vwlin/FleetTracker/src/gps.h

#include <driverlib/MSP430F5xx_6xx/gpio.h>
#include <msp430.h>
#include <stdio.h>
#include "SPI.h"

#define SAFEBOOT_DIRECTION           P6DIR
#define SAFEBOOT_PIN                 BIT4
#define SAFEBOOT_SELECT              P6SEL
#define SAFEBOOT_OUTPUT              P6OUT

#define GPS_CS_DIRECTION             P1DIR
#define GPS_CS_PIN                   BIT0
#define GPS_CS_SELECT                P1SEL
#define GPS_CS_OUTPUT                P1OUT

#define SET_SAFEBOOT_AS_GPIO         SAFEBOOT_SELECT &= ~SAFEBOOT_PIN
#define SET_SAFEBOOT_AS_OUTPUT       SAFEBOOT_DIRECTION |= SAFEBOOT_PIN
#define DRIVE_SAFEBOOT_PIN_HIGH      SAFEBOOT_OUTPUT |= SAFEBOOT_PIN
#define DRIVE_SAFEBOOT_PIN_LOW       SAFEBOOT_OUTPUT &= SAFEBOOT_PIN
#define TOGGLE_SAFEBOOT_PIN          SAFEBOOT_OUTPUT ^= SAFEBOOT_PIN

#define SET_GPS_CS_AS_GPIO           GPS_CS_SELECT &= ~GPS_CS_PIN
#define SET_GPS_CS_AS_OUTPUT         GPS_CS_DIRECTION |= GPS_CS_PIN
#define SELECT_GPS_CS                GPS_CS_OUTPUT &= ~GPS_CS_PIN //drive LOW
#define DESELECT_GPS_CS              GPS_CS_OUTPUT |= GPS_CS_PIN //drive HIGH


/* Configure_GPS
 * Drives safeboot high and initializes chip select
 */
void Configure_GPS();


/*~~~~~~~~~~~~~~~~~~~~~~~~~~~~~~~~~~~~~~
 * CONSTRUCT PACKETS
 ~~~~~~~~~~~~~~~~~~~~~~~~~~~~~~~~~~~~~*/

/*
 * ublox_configure_spi_port
 * Builds packet to configure SPI port of ublox module
 *
 * Parameters:
 *  returnPacket - array to be filled with send data
 */
void ublox_configure_spi_port(unsigned char* returnPacket);

/*
 * configure_ublox_nav_pvt
 * Builds packet to request data from ublox module
 *
 * Parameters:
 *  ublox_nav - array to be filled with send data
 */
void configure_ublox_nav_pvt(uint8_t* ublox_nav);

/*
 * configure_ublox_poll
 * Builds packet to configure requesting data from ublox module
 *
 * Parameters:
 *  ublox_poll - array to be filled with send data
 *  id1 - used to classify what to configure on ublox module
 *  id2 - used to classify what to configure on ublox module
 */
void configure_ublox_poll(uint8_t* ublox_poll, uint8_t id1, uint8_t id2);
