vwlin/FleetTracker/src/clock.c

/* --COPYRIGHT--,BSD
 * Copyright (c) 2017, Texas Instruments Incorporated
 * All rights reserved.
 *
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
 * *  Redistributions of source code must retain the above copyright
 *    notice, this list of conditions and the following disclaimer.
 *
 * *  Redistributions in binary form must reproduce the above copyright
 *    notice, this list of conditions and the following disclaimer in the
 *    documentation and/or other materials provided with the distribution.
 *
 * *  Neither the name of Texas Instruments Incorporated nor the names of
 *    its contributors may be used to endorse or promote products derived
 *    from this software without specific prior written permission.
 *
 * THIS SOFTWARE IS PROVIDED BY THE COPYRIGHT HOLDERS AND CONTRIBUTORS "AS IS"
 * AND ANY EXPRESS OR IMPLIED WARRANTIES, INCLUDING, BUT NOT LIMITED TO,
 * THE IMPLIED WARRANTIES OF MERCHANTABILITY AND FITNESS FOR A PARTICULAR
 * PURPOSE ARE DISCLAIMED. IN NO EVENT SHALL THE COPYRIGHT OWNER OR
 * CONTRIBUTORS BE LIABLE FOR ANY DIRECT, INDIRECT, INCIDENTAL, SPECIAL,
 * EXEMPLARY, OR CONSEQUENTIAL DAMAGES (INCLUDING, BUT NOT LIMITED TO,
 * PROCUREMENT OF SUBSTITUTE GOODS OR SERVICES; LOSS OF USE, DATA, OR PROFITS;
 * OR BUSINESS INTERRUPTION) HOWEVER CAUSED AND ON ANY THEORY OF LIABILITY,
 * WHETHER IN CONTRACT, STRICT LIABILITY, OR TORT (INCLUDING NEGLIGENCE OR
 * OTHERWISE) ARISING IN ANY WAY OUT OF THE USE OF THIS SOFTWARE,
 * EVEN IF ADVISED OF THE POSSIBILITY OF SUCH DAMAGE.
 * --/COPYRIGHT--*/

/*********************************************************************************
 * Set clock speed to 16 MHz
 */

//Variable to store status of Oscillator fault flags
//
//*****************************************************************************
#include "clock.h"
uint16_t status;

void Configure_Clock (void)
{
    // Set VCore
    PMM_setVCore(PMM_CORE_LEVEL_0);

    // Set DCO FLL reference = REFO
    UCS_initClockSignal(
        UCS_FLLREF,
        UCS_REFOCLK_SELECT,
        UCS_CLOCK_DIVIDER_1
        );
    // Set ACLK = REFO
    UCS_initClockSignal(
        UCS_ACLK,
        UCS_REFOCLK_SELECT,
        UCS_CLOCK_DIVIDER_1
        );

    // Set Ratio and Desired MCLK Frequency and initialize DCO
    UCS_initFLLSettle(
        UCS_MCLK_DESIRED_FREQUENCY_IN_KHZ,
        UCS_MCLK_FLLREF_RATIO
        );

    // Enable global oscillator fault flag
    SFR_clearInterrupt(SFR_OSCILLATOR_FAULT_INTERRUPT);
    SFR_enableInterrupt(SFR_OSCILLATOR_FAULT_INTERRUPT);

    // Enable global interrupt
    __bis_SR_register(GIE);

}


#if defined(__TI_COMPILER_VERSION__) || defined(__IAR_SYSTEMS_ICC__)
#pragma vector=UNMI_VECTOR
__interrupt
#elif defined(__GNUC__)
__attribute__((interrupt(UNMI_VECTOR)))
#endif
void NMI_ISR(void)
{
  do {
    // If it still can't clear the oscillator fault flags after the timeout, trap and wait here.
    status = UCS_clearAllOscFlagsWithTimeout(1000);
  } while(status != 0);
}
